zczqxc5/CASA0022-Dissertation-23-24/Code/Collect gesture data/sketch_may22a.ino

/* This code is for adding XIAO BLE Sense LSM6DS3 Accelerometer Raw Data */

#include "LSM6DS3.h"
#include "Wire.h"

//Create a instance of class LSM6DS3
LSM6DS3 myIMU(I2C_MODE, 0x6A);  //I2C device address 0x6A

#define CONVERT_G_TO_MS2 9.80665f
#define FREQUENCY_HZ 100
#define INTERVAL_MS (1000 / (FREQUENCY_HZ + 1))
#define DEG_TO_RAD 0.0174533f  // π / 180

static unsigned long last_interval_ms = 0;


void setup() {
  Serial.begin(115200);
  while (!Serial)
    ;

  if (myIMU.begin() != 0) {
    Serial.println("Device error");
  } else {
    Serial.println("Device OK!");
  }
}



void loop() {
  if (millis() > last_interval_ms + INTERVAL_MS) {
    last_interval_ms = millis();

    Serial.print(myIMU.readFloatAccelX() * CONVERT_G_TO_MS2, 4);
    Serial.print('\t');
    Serial.print(myIMU.readFloatAccelY() * CONVERT_G_TO_MS2, 4);
    Serial.print('\t');
    Serial.print(myIMU.readFloatAccelZ() * CONVERT_G_TO_MS2, 4);
    Serial.print('\t');
    Serial.print(myIMU.readFloatGyroX() * DEG_TO_RAD, 4);
    Serial.print('\t');
    Serial.print(myIMU.readFloatGyroY() * DEG_TO_RAD, 4);
    Serial.print('\t');
    Serial.println(myIMU.readFloatGyroZ() * DEG_TO_RAD, 4); 
  }
}
